Stanislav-developer/luxmeter_attiny85_oled/materials/Photo_1.jpg

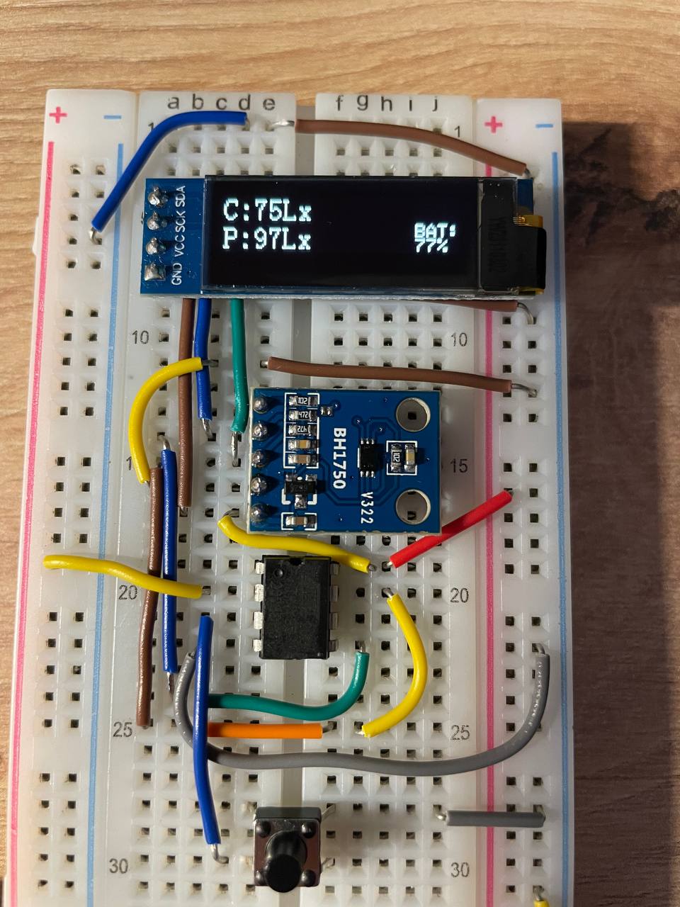
materials/Photo_1.jpg
