Stanislav-developer/luxmeter_attiny85_oled/materials/Photo_2.jpg

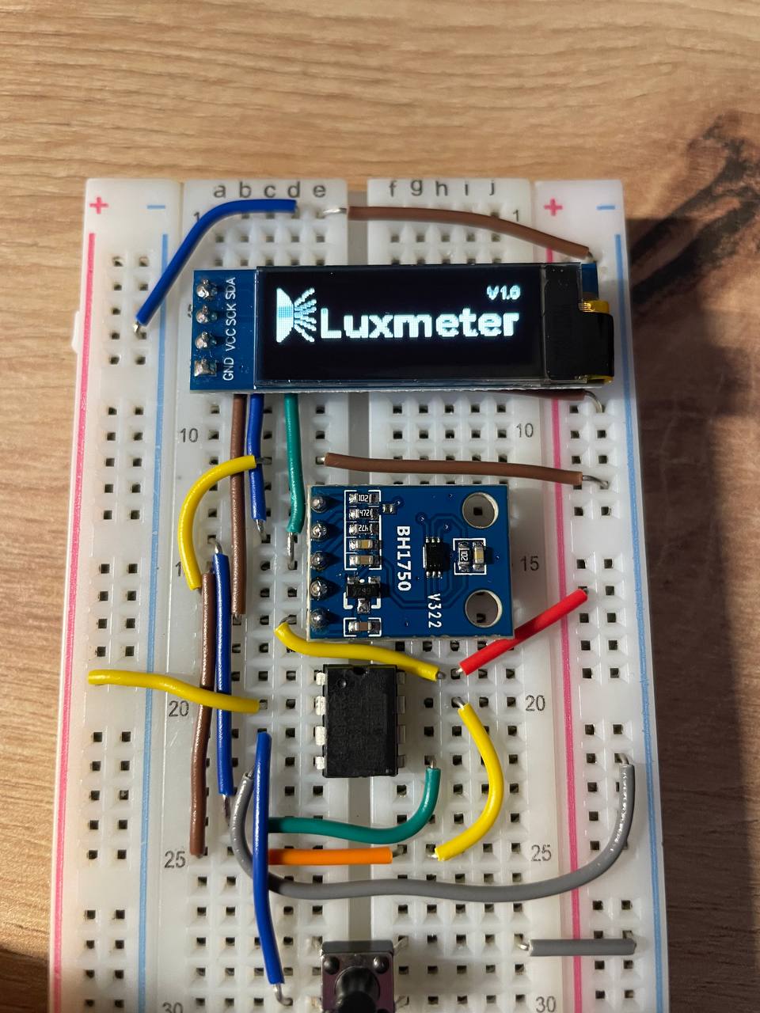
materials/Photo_2.jpg
